sumastavr/Generative_kAiBoard/Software/ESP32_PlatformIO/Generative_kAiboard_CouC/src/effects.h

//   Graphical effects to run on the RGB Shades LED array
//   Each function should have the following components:
//    * Must be declared void with no parameters or will break function pointer array
//    * Check effectInit, if false then init any required settings and set effectInit true
//    * Set effectDelay (the time in milliseconds until the next run of this effect)
//    * All animation should be controlled with counters and effectDelay, no delay() or loops
//    * Pixel data should be written using leds[XY(x,y)] to map coordinates to the RGB Shades layout

// Triple Sine Waves
void threeSine() {

  static byte sineOffset = 0; // counter for current position of sine waves

  // startup tasks
  if (effectInit == false) {
    effectInit = true;
    effectDelay = 20;
  }

  // Draw one frame of the animation into the LED array
  for (byte x = 0; x < kMatrixWidth; x++) {
    for (int y = 0; y < kMatrixHeight; y++) {

      // Calculate "sine" waves with varying periods
      // sin8 is used for speed; cos8, quadwave8, or triwave8 would also work here
      byte sinDistanceR = qmul8(abs(y * (255 / kMatrixHeight) - sin8(sineOffset * 9 + x * 16)), 2);
      byte sinDistanceG = qmul8(abs(y * (255 / kMatrixHeight) - sin8(sineOffset * 10 + x * 16)), 2);
      byte sinDistanceB = qmul8(abs(y * (255 / kMatrixHeight) - sin8(sineOffset * 11 + x * 16)), 2);

      leds[XY(x, y)] = CRGB(255 - sinDistanceR, 255 - sinDistanceG, 255 - sinDistanceB);
    }
  }

  sineOffset++; // byte will wrap from 255 to 0, matching sin8 0-255 cycle

}


// RGB Plasma
void plasma() {

  static byte offset  = 0; // counter for radial color wave motion
  static int plasVector = 0; // counter for orbiting plasma center

  // startup tasks
  if (effectInit == false) {
    effectInit = true;
    effectDelay = 10;
  }

  // Calculate current center of plasma pattern (can be offscreen)
  int xOffset = cos8(plasVector / 256);
  int yOffset = sin8(plasVector / 256);

  // Draw one frame of the animation into the LED array
  for (int x = 0; x < kMatrixWidth; x++) {
    for (int y = 0; y < kMatrixHeight; y++) {
      byte color = sin8(sqrt(sq(((float)x - 7.5) * 10 + xOffset - 127) + sq(((float)y - 2) * 10 + yOffset - 127)) + offset);
      leds[XY(x, y)] = CHSV(color, 255, 255);
    }
  }

  offset++; // wraps at 255 for sin8
  plasVector += 16; // using an int for slower orbit (wraps at 65536)

}


// Scanning pattern left/right, uses global hue cycle
void rider() {

  static byte riderPos = 0;

  // startup tasks
  if (effectInit == false) {
    effectInit = true;
    effectDelay = 5;
    riderPos = 0;
  }

  // Draw one frame of the animation into the LED array
  for (byte x = 0; x < kMatrixWidth; x++) {
    int brightness = abs(x * (256 / kMatrixWidth) - triwave8(riderPos) * 2 + 127) * 3;
    if (brightness > 255) brightness = 255;
    brightness = 255 - brightness;
    CRGB riderColor = CHSV(cycleHue, 255, brightness);
    for (byte y = 0; y < kMatrixHeight; y++) {
      leds[XY(x, y)] = riderColor;
    }
  }

  riderPos++; // byte wraps to 0 at 255, triwave8 is also 0-255 periodic

}


// Shimmering noise, uses global hue cycle
void glitter() {

  // startup tasks
  if (effectInit == false) {
    effectInit = true;
    effectDelay = 15;
  }

  // Draw one frame of the animation into the LED array
  for (int x = 0; x < kMatrixWidth; x++) {
    for (int y = 0; y < kMatrixHeight; y++) {
      leds[XY(x, y)] = CHSV(cycleHue, 255, random8(5) * 63);
    }
  }

}


// Fills saturated colors into the array from alternating directions
void colorFill() {

  static byte currentColor = 0;
  static byte currentRow = 0;
  static byte currentDirection = 0;

  // startup tasks
  if (effectInit == false) {
    effectInit = true;
    effectDelay = 45;
    currentColor = 0;
    currentRow = 0;
    currentDirection = 0;
    currentPalette = RainbowColors_p;
  }

  // test a bitmask to fill up or down when currentDirection is 0 or 2 (0b00 or 0b10)
  if (!(currentDirection & 1)) {
    effectDelay = 45; // slower since vertical has fewer pixels
    for (byte x = 0; x < kMatrixWidth; x++) {
      byte y = currentRow;
      if (currentDirection == 2) y = kMatrixHeight - 1 - currentRow;
      leds[XY(x, y)] = currentPalette[currentColor];
    }
  }

  // test a bitmask to fill left or right when currentDirection is 1 or 3 (0b01 or 0b11)
  if (currentDirection & 1) {
    effectDelay = 20; // faster since horizontal has more pixels
    for (byte y = 0; y < kMatrixHeight; y++) {
      byte x = currentRow;
      if (currentDirection == 3) x = kMatrixWidth - 1 - currentRow;
      leds[XY(x, y)] = currentPalette[currentColor];
    }
  }

  currentRow++;

  // detect when a fill is complete, change color and direction
  if ((!(currentDirection & 1) && currentRow >= kMatrixHeight) || ((currentDirection & 1) && currentRow >= kMatrixWidth)) {
    currentRow = 0;
    currentColor += random8(3, 6);
    if (currentColor > 15) currentColor -= 16;
    currentDirection++;
    if (currentDirection > 3) currentDirection = 0;
    effectDelay = 300; // wait a little bit longer after completing a fill
  }


}

// Emulate 3D anaglyph glasses
void threeDee() {

  // startup tasks
  if (effectInit == false) {
    effectInit = true;
    effectDelay = 50;
  }

  for (byte x = 0; x < kMatrixWidth; x++) {
    for (byte y = 0; y < kMatrixHeight; y++) {
      if (x < 7) {
        leds[XY(x, y)] = CRGB::Blue;
      } else if (x > 8) {
        leds[XY(x, y)] = CRGB::Red;
      } else {
        leds[XY(x, y)] = CRGB::Black;
      }
    }
  }

  leds[XY(6, 0)] = CRGB::Black;
  leds[XY(9, 0)] = CRGB::Black;

}

// Random pixels scroll sideways, uses current hue
#define rainDir 0
void sideRain() {

  // startup tasks
  if (effectInit == false) {
    effectInit = true;
    effectDelay = 30;
  }

  scrollArray(rainDir);
  byte randPixel = random8(kMatrixHeight);
  for (byte y = 0; y < kMatrixHeight; y++) leds[XY((kMatrixWidth - 1) * rainDir, y)] = CRGB::Black;
  leds[XY((kMatrixWidth - 1)*rainDir, randPixel)] = CHSV(cycleHue, 255, 255);

}

// Pixels with random locations and random colors selected from a palette
// Use with the fadeAll function to allow old pixels to decay
void confetti() {

  // startup tasks
  if (effectInit == false) {
    effectInit = true;
    effectDelay = 10;
    selectRandomPalette();
  }

  // scatter random colored pixels at several random coordinates
  for (byte i = 0; i < 2; i++) {
    int xpos=random16(kMatrixWidth);
    int ypos=random16(kMatrixHeight);
    //Serial.println(XY(xpos,ypos));
    //leds[XY(xpos, ypos)] = ColorFromPalette(currentPalette, random16(255), 255); //CHSV(random16(255), 255, 255);
    leds[XY(xpos, ypos)] = CHSV(random16(255), 255, 255);
    random16_add_entropy(1);
  }

}


// Draw slanting bars scrolling across the array, uses current hue
void slantBars() {

  static byte slantPos = 0;

  // startup tasks
  if (effectInit == false) {
    effectInit = true;
    effectDelay = 5;
  }

  for (byte x = 0; x < kMatrixWidth; x++) {
    for (byte y = 0; y < kMatrixHeight; y++) {
      leds[XY(x, y)] = CHSV(cycleHue, 255, quadwave8(x * 32 + y * 32 + slantPos));
    }
  }

  slantPos -= 4;

}


#define NORMAL 0
#define RAINBOW 1
#define charSpacing 2
// Scroll a text string
void scrollText(byte message, byte style, CRGB fgColor, CRGB bgColor) {
  static byte currentMessageChar = 0;
  static byte currentCharColumn = 0;
  static byte paletteCycle = 0;
  static CRGB currentColor;
  static byte bitBuffer[48] = {0};
  static byte bitBufferPointer = 0;

  // startup tasks
  if (effectInit == false) {
    effectInit = true;
    effectDelay = 35;
    currentMessageChar = 0;
    currentCharColumn = 0;
    selectFlashString(message);
    loadCharBuffer(loadStringChar(message, currentMessageChar));
    currentPalette = RainbowColors_p;
    for (byte i = 0; i < kMatrixWidth; i++) bitBuffer[i] = 0;
  }

  paletteCycle += 15;

  if (currentCharColumn < 5) { // characters are 5 pixels wide
    bitBuffer[(bitBufferPointer + kMatrixWidth - 1) % kMatrixWidth] = charBuffer[currentCharColumn]; // character
  } else {
    bitBuffer[(bitBufferPointer + kMatrixWidth - 1) % kMatrixWidth] = 0; // space
  }

  CRGB pixelColor;
  for (byte x = 0; x < kMatrixWidth; x++) {
    for (byte y = 0; y < 5; y++) { // characters are 5 pixels tall
      if (bitRead(bitBuffer[(bitBufferPointer + x) % kMatrixWidth], y) == 1) {
        if (style == RAINBOW) {
         // pixelColor = ColorFromPalette(currentPalette, paletteCycle+y*16, 255);
         pixelColor = ColorFromPalette(currentPalette, paletteCycle+y*16, 255);
        
        } else {
          pixelColor = fgColor;
        }
      } else {
        pixelColor = bgColor;
      }
      leds[XY(x, y)] = pixelColor;
    }
  }

  currentCharColumn++;
  if (currentCharColumn > (4 + charSpacing)) {
    currentCharColumn = 0;
    currentMessageChar++;
    char nextChar = loadStringChar(message, currentMessageChar);
    if (nextChar == 0) { // null character at end of strong
      currentMessageChar = 0;
      nextChar = loadStringChar(message, currentMessageChar);
    }
    loadCharBuffer(nextChar);
  }

  bitBufferPointer++;
  if (bitBufferPointer > 47) bitBufferPointer = 0;

}


void scrollTextZero() {
  scrollText(0, NORMAL, CRGB::Red, CRGB::Black);
}

void scrollTextOne() {
  scrollText(1, RAINBOW, 0, CRGB::Black);
}

void scrollTextTwo() {
  scrollText(2, NORMAL, CRGB::Green, CRGB(0,0,8));
}

void brexit(){
  scrollText(1, RAINBOW, 0, CRGB::Black);  
}

void todoList(){
  uint8_t banner[]={0,1,2,3,8,11,15,19,25,28,32,36,40};
  uint8_t done[]={9,10,13,16,17,18,20,21,22,23,24,29,31,33,34,35,37};
  uint8_t hold[]={};
  uint8_t nope[]={4,5,6,7,10,14,26,27,30,38,39,41,42};

    
    for (int x=0;x<sizeof(banner)/sizeof(banner[0]);x++){
      if(currentEffect==banner[x]){
        scrollText(currentEffect, RAINBOW, 0, CRGB::Black); 
      }
    }

    for (int x=0;x<sizeof(done)/sizeof(done[0]);x++){
      if(currentEffect==done[x]){
         scrollText(currentEffect, NORMAL, CRGB::Green, CRGB(0,0,8));
      }
    }

    for (int x=0;x<sizeof(nope)/sizeof(nope[0]);x++){
      if(currentEffect==nope[x]){
        scrollText(currentEffect, NORMAL, CRGB::Red, CRGB::Black);
      }
    }

    for (int x=0;x<sizeof(hold)/sizeof(hold[0]);x++){
      if(currentEffect==hold[x]){
        scrollText(currentEffect, NORMAL, CRGB::Blue, CRGB::Black);
      }
    }
    
 
}
