sumastavr/Generative_kAiBoard/Software/STM32_PlatformIO/Generative_kAiboard/src/NFC.h

/*

BSD 3-Clause License

Copyright (c) 2023, Pamungkas Sumasta (www.sumasta.tech)

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
1. Redistributions of source code must retain the above copyright notice, this
   list of conditions and the following disclaimer.

2. Redistributions in binary form must reproduce the above copyright notice,
   this list of conditions and the following disclaimer in the documentation
   and/or other materials provided with the distribution.

3. Neither the name of the copyright holder nor the names of its
   contributors may be used to endorse or promote products derived from
   this software without specific prior written permission.

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
*/

#include <Adafruit_PN532.h>

// Or use this line for a breakout or shield with an I2C connection:
Adafruit_PN532 nfc(PN532_IRQ, PN532_RESET);

bool NFCInitialized=false;

bool initNFC(){
  nfc.begin();

  uint32_t versiondata = nfc.getFirmwareVersion();
  if (! versiondata) {
    Serial.print("Didn't find PN53x board");
    NFCInitialized=false;
    return 0;
  }
  // Got ok data, print it out!
  Serial.print("Found chip PN5"); Serial.println((versiondata>>24) & 0xFF, HEX);
  Serial.print("Firmware ver. "); Serial.print((versiondata>>16) & 0xFF, DEC);
  Serial.print('.'); Serial.println((versiondata>>8) & 0xFF, DEC);
  NFCInitialized=true;
  return 1;
}

bool scanNFC(){
  
  // put your main code here, to run repeatedly:
  
  bool success;
  bool validated=false;
  uint8_t uid[] = { 0, 0, 0, 0, 0, 0, 0 };  // Buffer to store the returned UID
  uint8_t uidLength;                        // Length of the UID (4 or 7 bytes depending on ISO14443A card type)

  // Wait for an ISO14443A type cards (Mifare, etc.).  When one is found
  // 'uid' will be populated with the UID, and uidLength will indicate
  // if the uid is 4 bytes (Mifare Classic) or 7 bytes (Mifare Ultralight)
  success = nfc.readPassiveTargetID(PN532_MIFARE_ISO14443A, uid, &uidLength,200);

  if (success) {
    // Display some basic information about the card
    Serial.println("Found an ISO14443A card");
    Serial.print("  UID Length: ");Serial.print(uidLength, DEC);Serial.println(" bytes");
    Serial.print("  UID Value: ");
    nfc.PrintHex(uid, uidLength);
    Serial.println("");

    if (uidLength == 7){
      // We probably have a Mifare Ultralight card ...
      Serial.println("Seems to be a Mifare Ultralight tag (7 byte UID)");
      Serial.println(uid[0],HEX);
      Serial.println(uid[1],HEX);
      Serial.println(uid[2],HEX);
      Serial.println(uid[3],HEX);
      Serial.println(uid[4],HEX);
      Serial.println(uid[5],HEX);

      if (uid[0]==0x04 && uid[1]==0xc3 && uid[2]==0x1f && uid[3]==0x4a && uid[4]==0x11 && uid[5]==0x3c && uid[6]==0x80){
        validated=true;
        return validated;
      }

      /*
      // Try to read the first general-purpose user page (#4)
      Serial.println("Reading page 4");
      uint8_t data[32];
      success = nfc.mifareultralight_ReadPage (4, data);
      if (success)
      {
        // Data seems to have been read ... spit it out
        nfc.PrintHexChar(data, 4);
        Serial.println("");

        // Wait a bit before reading the card again
        delay(1000);
      }
      else
      {
        Serial.println("Ooops ... unable to read the requested page!?");
      }
      */
    }
  }
  return false;
}

  #ifdef USE_NFC
    nfc.begin();

    uint32_t versiondata = nfc.getFirmwareVersion();
    if (! versiondata) {
      Serial.print("Didn't find PN53x board");
      while (1); // halt
    }
    // Got ok data, print it out!
    Serial.print("Found chip PN5"); Serial.println((versiondata>>24) & 0xFF, HEX);
    Serial.print("Firmware ver. "); Serial.print((versiondata>>16) & 0xFF, DEC);
    Serial.print('.'); Serial.println((versiondata>>8) & 0xFF, DEC);

    Serial.println("Waiting for an ISO14443A Card ...");
  #endif
