sumastavr/Generative_kAiBoard/Software/STM32_PlatformIO/Generative_kAiboard/src/trust_anchors.h

/*

BSD 3-Clause License

Copyright (c) 2023, Pamungkas Sumasta (www.sumasta.tech)

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
1. Redistributions of source code must retain the above copyright notice, this
   list of conditions and the following disclaimer.

2. Redistributions in binary form must reproduce the above copyright notice,
   this list of conditions and the following disclaimer in the documentation
   and/or other materials provided with the distribution.

3. Neither the name of the copyright holder nor the names of its
   contributors may be used to endorse or promote products derived from
   this software without specific prior written permission.

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
*/

#ifndef _CERTIFICATES_H_
#define _CERTIFICATES_H_

#ifdef __cplusplus
extern "C"
{
#endif

/* This file is auto-generated by the pycert_bearssl tool.  Do not change it manually.
 * Certificates are BearSSL br_x509_trust_anchor format.  Included certs:
 *
 * Index:    0
 * Label:    Baltimore CyberTrust Root
 * Subject:  CN=Baltimore CyberTrust Root,OU=CyberTrust,O=Baltimore,C=IE
 * Domain(s): api.openai.com
 */

#define TAs_NUM 1

static const unsigned char TA_DN0[] = {
    0x30, 0x5a, 0x31, 0x0b, 0x30, 0x09, 0x06, 0x03, 0x55, 0x04, 0x06, 0x13,
    0x02, 0x49, 0x45, 0x31, 0x12, 0x30, 0x10, 0x06, 0x03, 0x55, 0x04, 0x0a,
    0x13, 0x09, 0x42, 0x61, 0x6c, 0x74, 0x69, 0x6d, 0x6f, 0x72, 0x65, 0x31,
    0x13, 0x30, 0x11, 0x06, 0x03, 0x55, 0x04, 0x0b, 0x13, 0x0a, 0x43, 0x79,
    0x62, 0x65, 0x72, 0x54, 0x72, 0x75, 0x73, 0x74, 0x31, 0x22, 0x30, 0x20,
    0x06, 0x03, 0x55, 0x04, 0x03, 0x13, 0x19, 0x42, 0x61, 0x6c, 0x74, 0x69,
    0x6d, 0x6f, 0x72, 0x65, 0x20, 0x43, 0x79, 0x62, 0x65, 0x72, 0x54, 0x72,
    0x75, 0x73, 0x74, 0x20, 0x52, 0x6f, 0x6f, 0x74,
};

static const unsigned char TA_RSA_N0[] = {
    0xa3, 0x04, 0xbb, 0x22, 0xab, 0x98, 0x3d, 0x57, 0xe8, 0x26, 0x72, 0x9a,
    0xb5, 0x79, 0xd4, 0x29, 0xe2, 0xe1, 0xe8, 0x95, 0x80, 0xb1, 0xb0, 0xe3,
    0x5b, 0x8e, 0x2b, 0x29, 0x9a, 0x64, 0xdf, 0xa1, 0x5d, 0xed, 0xb0, 0x09,
    0x05, 0x6d, 0xdb, 0x28, 0x2e, 0xce, 0x62, 0xa2, 0x62, 0xfe, 0xb4, 0x88,
    0xda, 0x12, 0xeb, 0x38, 0xeb, 0x21, 0x9d, 0xc0, 0x41, 0x2b, 0x01, 0x52,
    0x7b, 0x88, 0x77, 0xd3, 0x1c, 0x8f, 0xc7, 0xba, 0xb9, 0x88, 0xb5, 0x6a,
    0x09, 0xe7, 0x73, 0xe8, 0x11, 0x40, 0xa7, 0xd1, 0xcc, 0xca, 0x62, 0x8d,
    0x2d, 0xe5, 0x8f, 0x0b, 0xa6, 0x50, 0xd2, 0xa8, 0x50, 0xc3, 0x28, 0xea,
    0xf5, 0xab, 0x25, 0x87, 0x8a, 0x9a, 0x96, 0x1c, 0xa9, 0x67, 0xb8, 0x3f,
    0x0c, 0xd5, 0xf7, 0xf9, 0x52, 0x13, 0x2f, 0xc2, 0x1b, 0xd5, 0x70, 0x70,
    0xf0, 0x8f, 0xc0, 0x12, 0xca, 0x06, 0xcb, 0x9a, 0xe1, 0xd9, 0xca, 0x33,
    0x7a, 0x77, 0xd6, 0xf8, 0xec, 0xb9, 0xf1, 0x68, 0x44, 0x42, 0x48, 0x13,
    0xd2, 0xc0, 0xc2, 0xa4, 0xae, 0x5e, 0x60, 0xfe, 0xb6, 0xa6, 0x05, 0xfc,
    0xb4, 0xdd, 0x07, 0x59, 0x02, 0xd4, 0x59, 0x18, 0x98, 0x63, 0xf5, 0xa5,
    0x63, 0xe0, 0x90, 0x0c, 0x7d, 0x5d, 0xb2, 0x06, 0x7a, 0xf3, 0x85, 0xea,
    0xeb, 0xd4, 0x03, 0xae, 0x5e, 0x84, 0x3e, 0x5f, 0xff, 0x15, 0xed, 0x69,
    0xbc, 0xf9, 0x39, 0x36, 0x72, 0x75, 0xcf, 0x77, 0x52, 0x4d, 0xf3, 0xc9,
    0x90, 0x2c, 0xb9, 0x3d, 0xe5, 0xc9, 0x23, 0x53, 0x3f, 0x1f, 0x24, 0x98,
    0x21, 0x5c, 0x07, 0x99, 0x29, 0xbd, 0xc6, 0x3a, 0xec, 0xe7, 0x6e, 0x86,
    0x3a, 0x6b, 0x97, 0x74, 0x63, 0x33, 0xbd, 0x68, 0x18, 0x31, 0xf0, 0x78,
    0x8d, 0x76, 0xbf, 0xfc, 0x9e, 0x8e, 0x5d, 0x2a, 0x86, 0xa7, 0x4d, 0x90,
    0xdc, 0x27, 0x1a, 0x39,
};

static const unsigned char TA_RSA_E0[] = {
    0x01, 0x00, 0x01,
};

static const br_x509_trust_anchor TAs[] = {
    {
        { (unsigned char *)TA_DN0, sizeof TA_DN0 },
        BR_X509_TA_CA,
        {
            BR_KEYTYPE_RSA,
            { .rsa = {
                (unsigned char *)TA_RSA_N0, sizeof TA_RSA_N0,
                (unsigned char *)TA_RSA_E0, sizeof TA_RSA_E0,
            } }
        }
    },
};

#ifdef __cplusplus
} /* extern "C" */
#endif

#endif /* ifndef _CERTIFICATES_H_ */
